chayakornk24/triangular-taper-line/simulation/comparison/netlist_vs_geometry_expanded.png

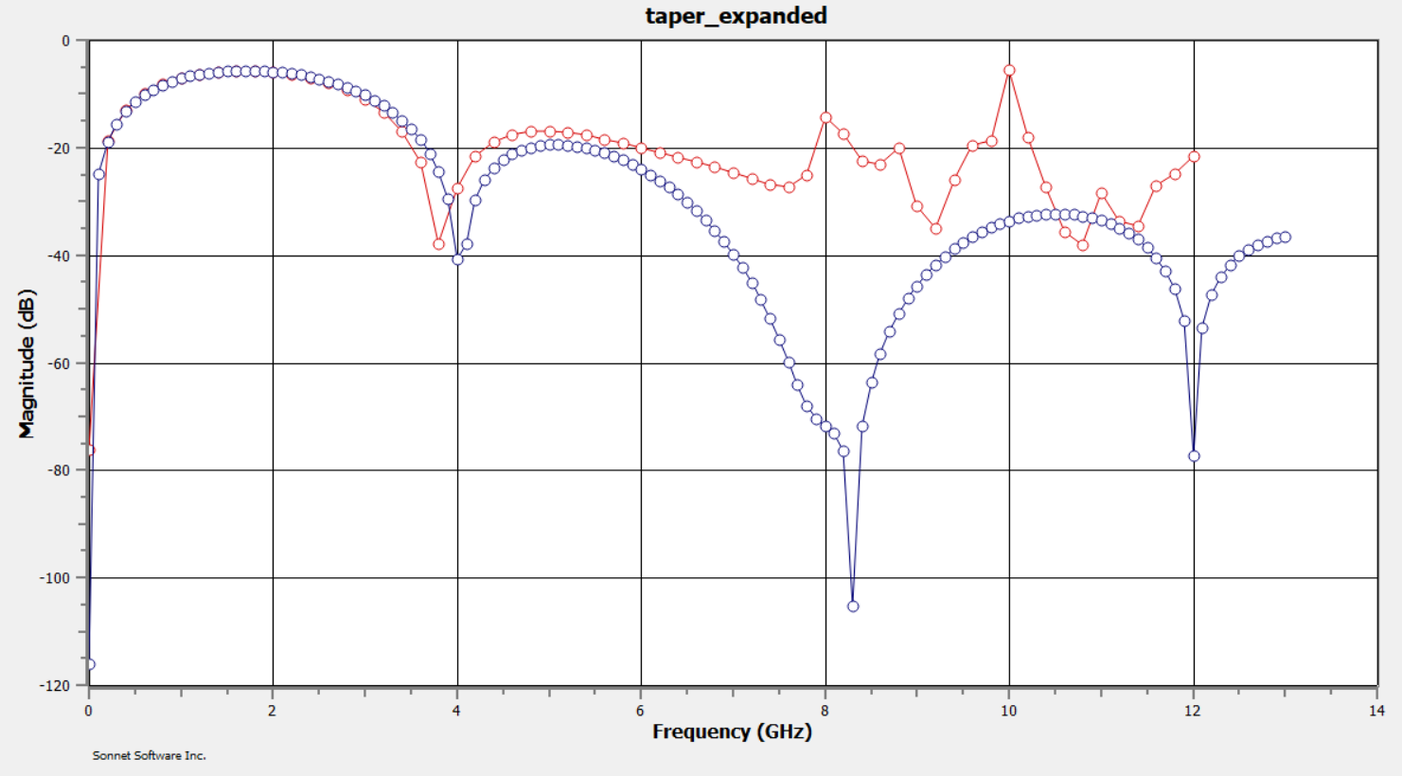
simulation/comparison/netlist_vs_geometry_expanded.png
