chayakornk24/triangular-taper-line/simulation/comparison/netlist_vs_geometry_original in Magnitude .png

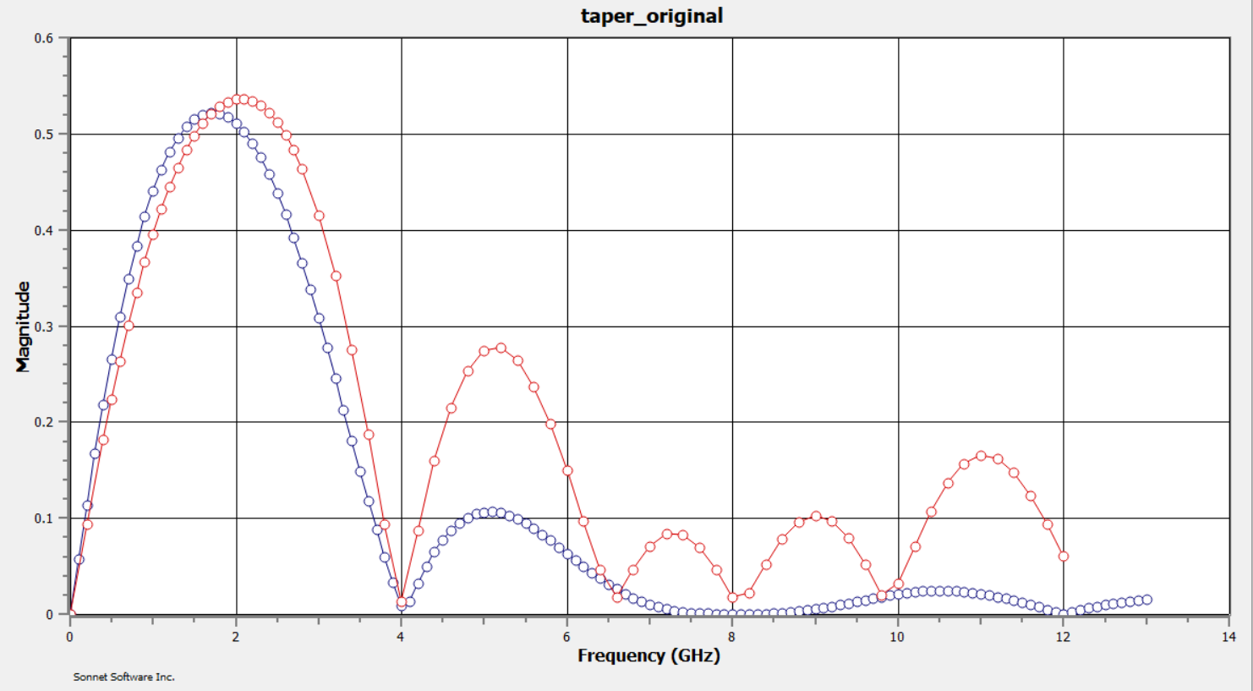
simulation/comparison/netlist_vs_geometry_original in Magnitude .png
