chayakornk24/triangular-taper-line/simulation/simulation/geometry/simulation/geometry/original_box/Tapersimulationoriginal(Magnitude).png

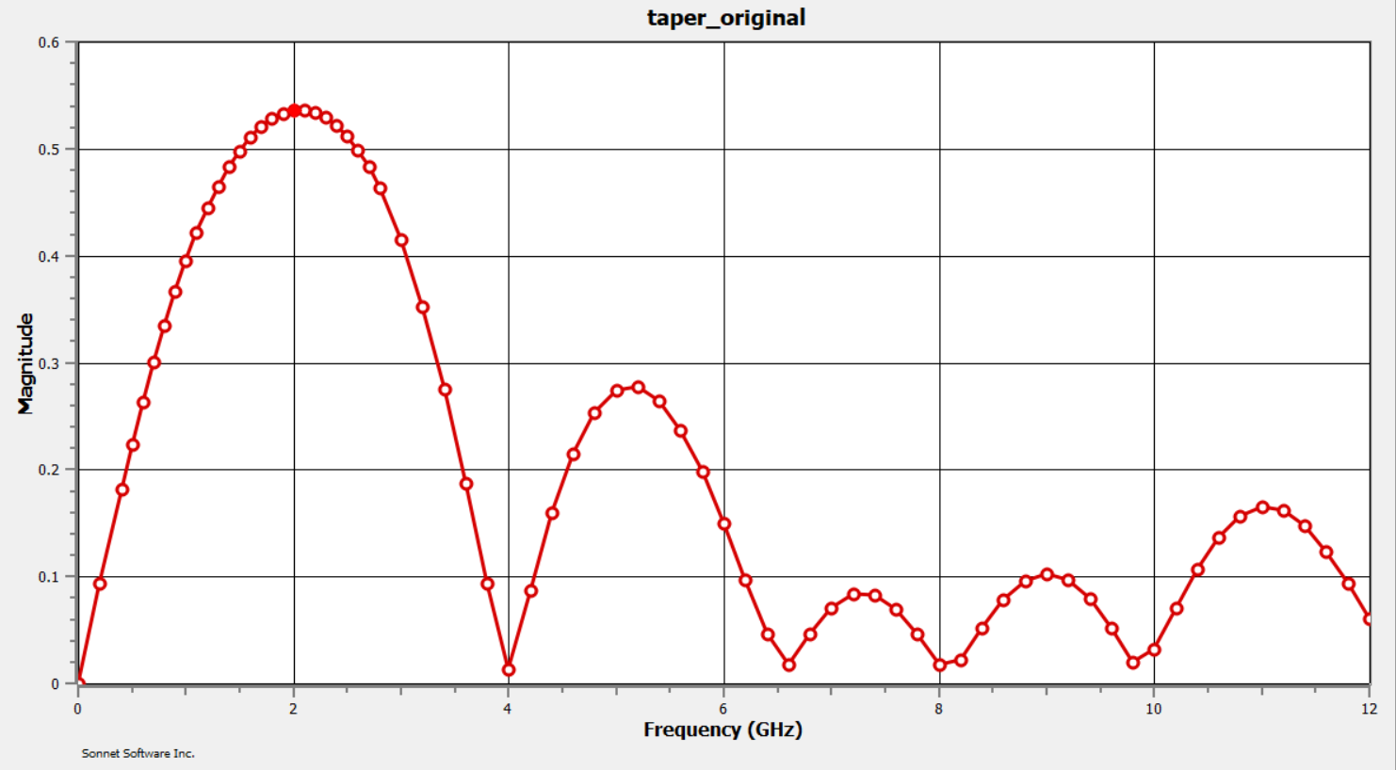
simulation/simulation/geometry/simulation/geometry/original_box/Tapersimulationoriginal(Magnitude).png
