chayakornk24/triangular-taper-line/simulation/simulation/netlist/simulation/netlist/10_sections_50to100/10_sections_50to100 ( dB ).png

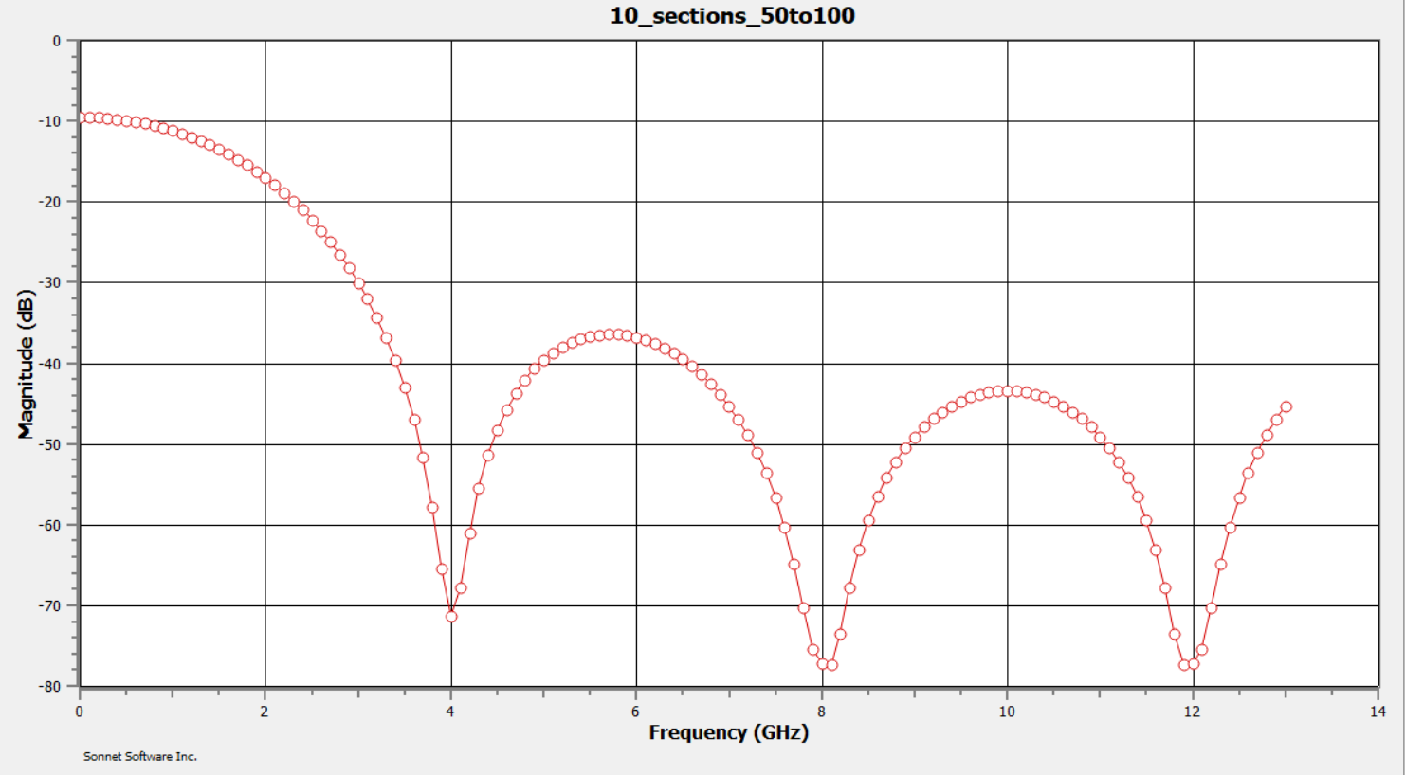
simulation/simulation/netlist/simulation/netlist/10_sections_50to100/10_sections_50to100 ( dB ).png
