chayakornk24/triangular-taper-line/simulation/simulation/netlist/simulation/netlist/20_sections_50to100to50/20_sections_50to100to50 ( Magnitude ).png

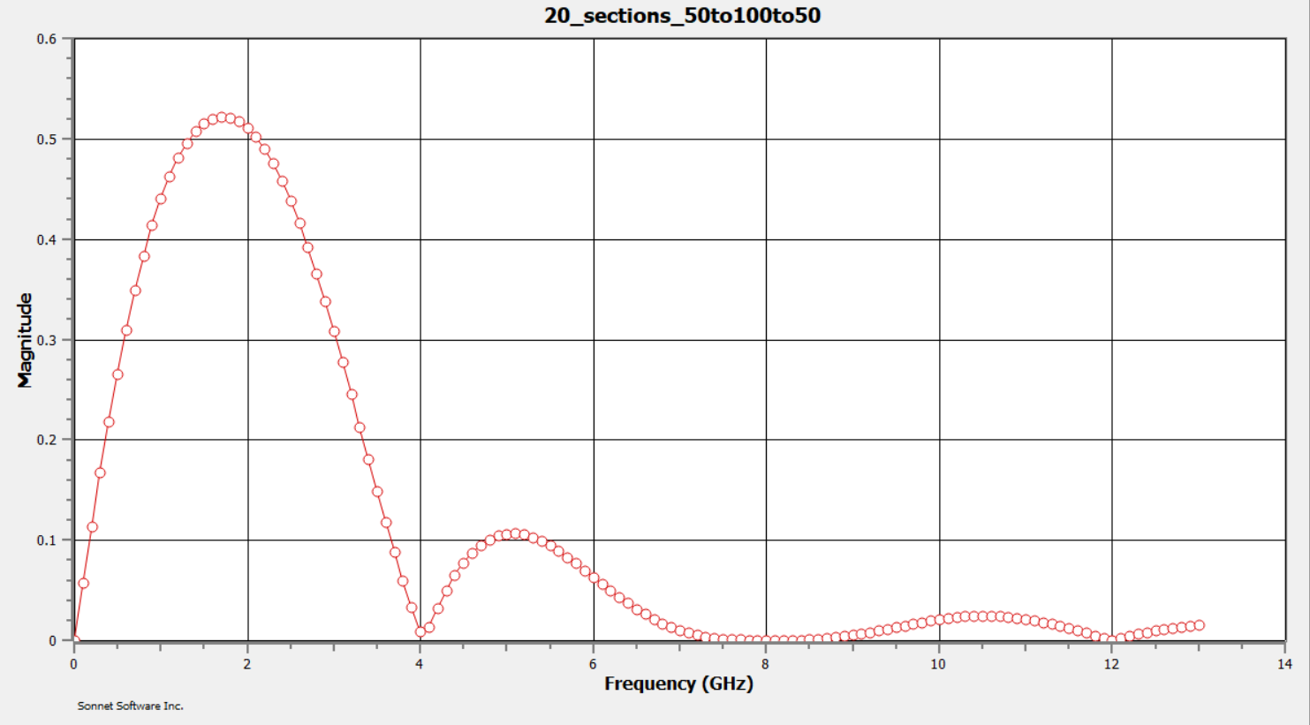
simulation/simulation/netlist/simulation/netlist/20_sections_50to100to50/20_sections_50to100to50 ( Magnitude ).png
