chayakornk24/triangular-taper-line/measurement/measurement_plot.png

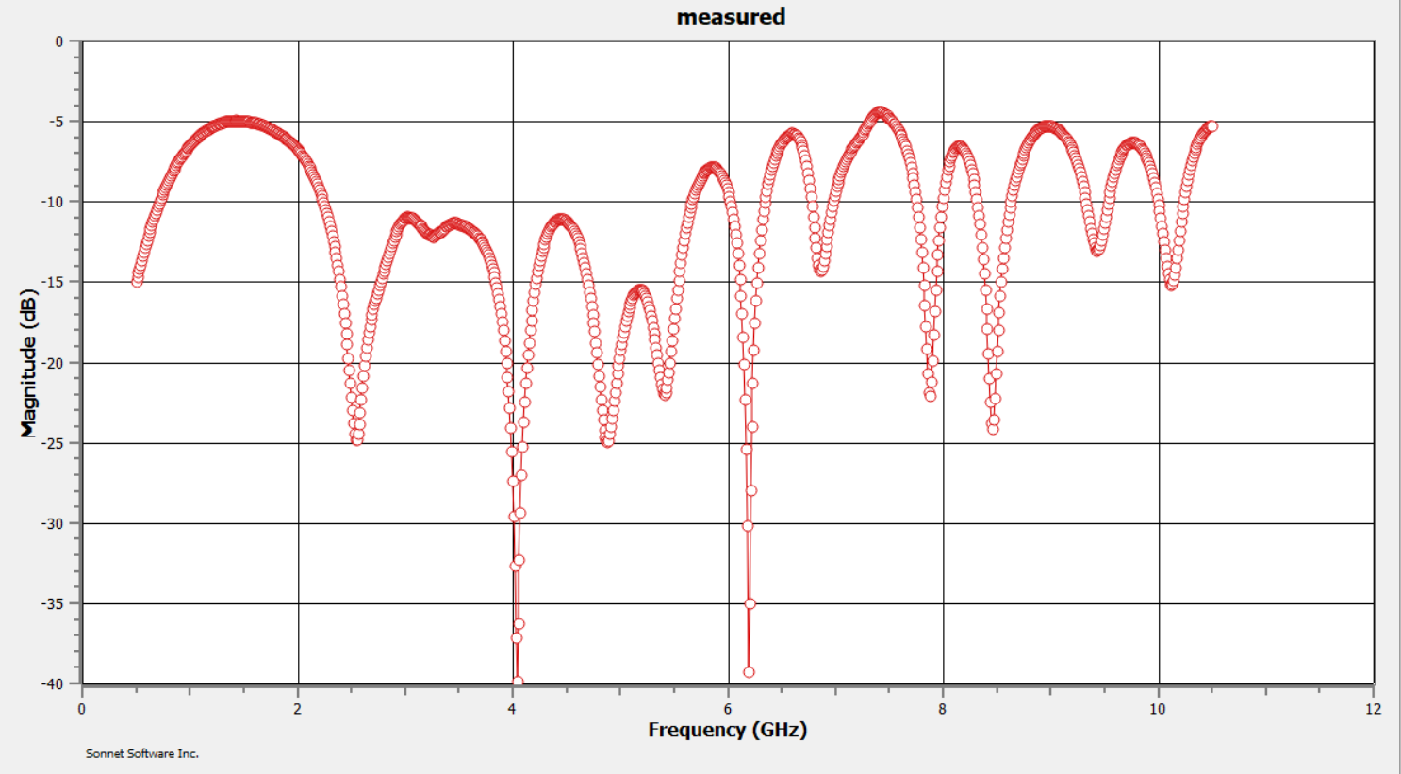
measurement/measurement_plot.png
